choubbikeyboards/scaffold/front.jpg

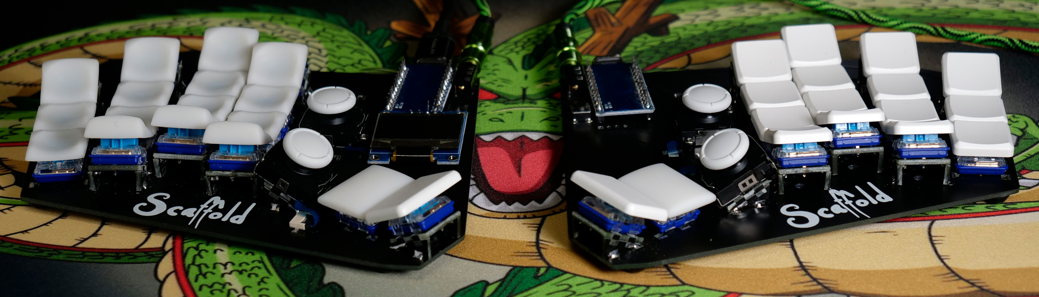
front.jpg
